LightestDark/The-Twins/PCB/Split Keyboard.kicad_sch

## KiCad design PCB/Split Keyboard.kicad_sch (2025-12-27)

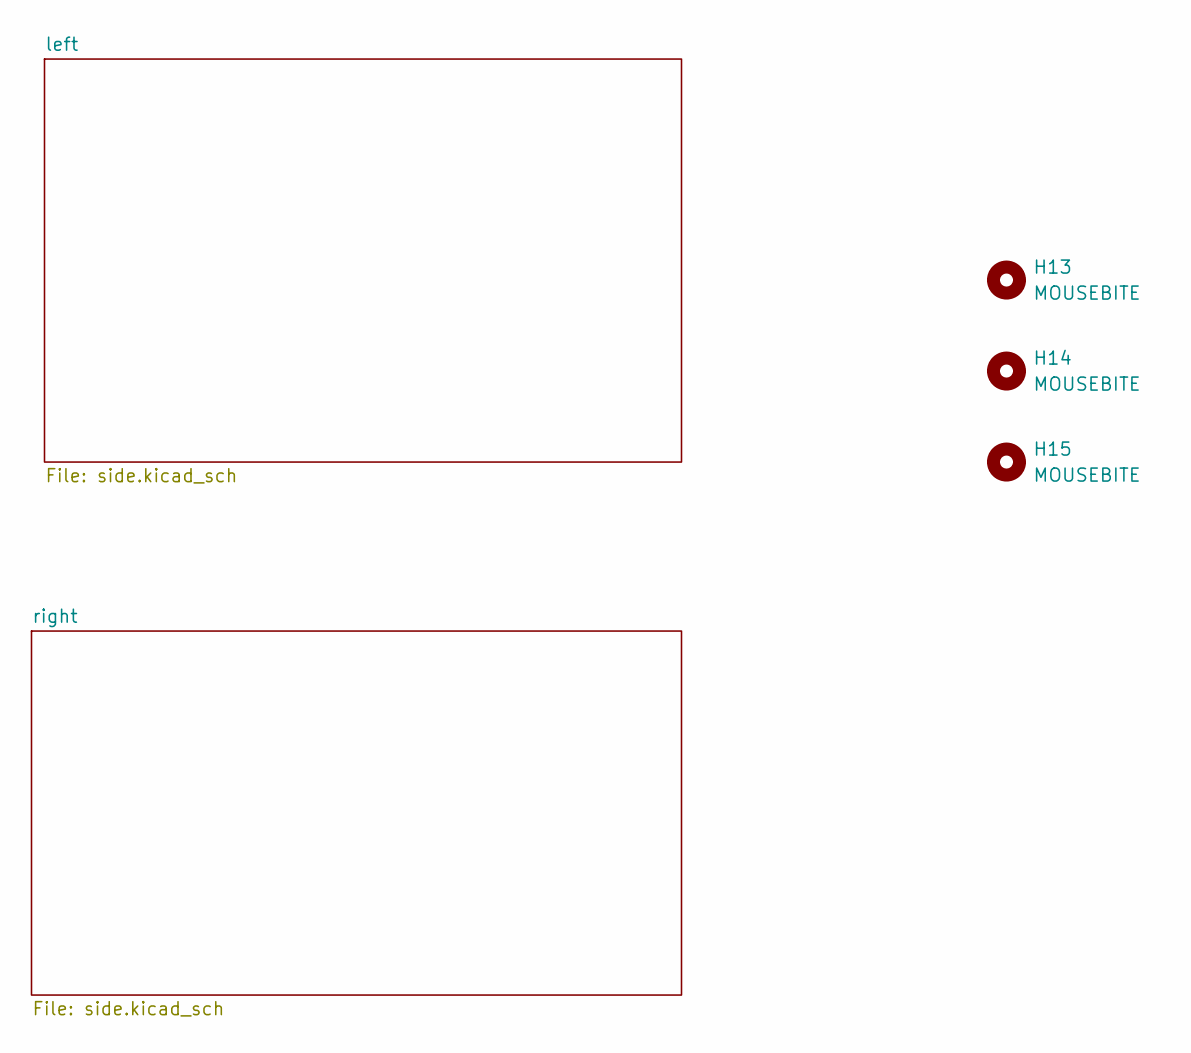
[picture p2: schematic Split Keyboard.kicad_sch]

Parts:
H13, H14, H15: MOUSEBITE; MouseBite-Slot_2.54x5.08mm_on-edge_D0.5mm_P0.85mm_5h_Trace
